ChristopherBrown200/f1-track-status-sign/3D Print Files/Tracks/Baku.stl

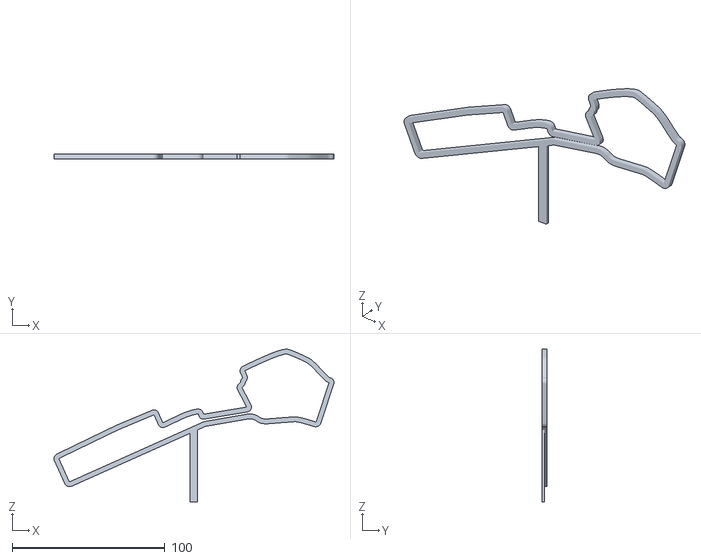
[picture p16: CAD file, 2026-06-22]
3D Print Files/Tracks/Baku.stl
183.3 x 3.00 x 100.0
