ChristopherBrown200/f1-track-status-sign/3D Print Files/Tracks/Gilles-Villeneuve.stl

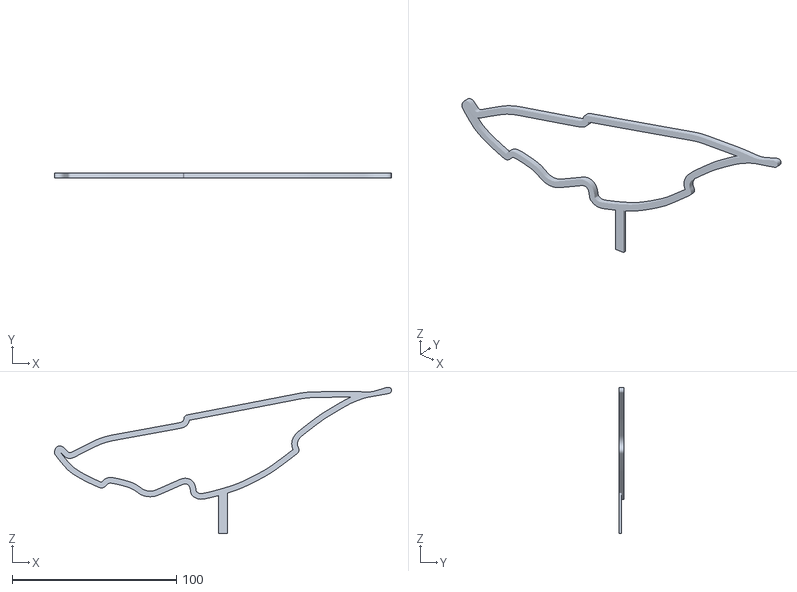
[picture p17: CAD file, 2026-06-22]
3D Print Files/Tracks/Gilles-Villeneuve.stl
204.9 x 3.00 x 89.0
