ChristopherBrown200/f1-track-status-sign/3D Print Files/Tracks/Zandvoort.stl

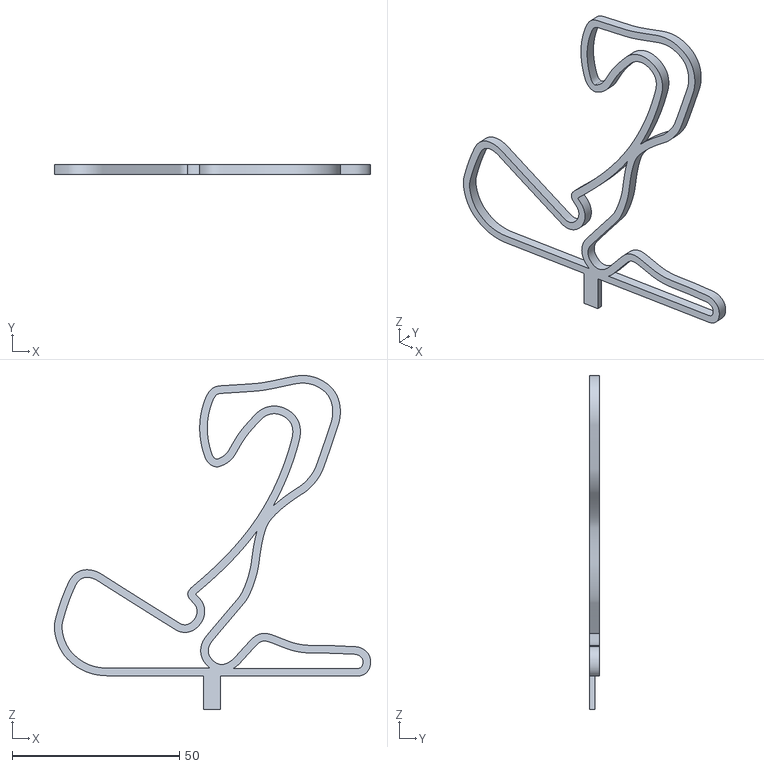
[picture p18: CAD file, 2026-06-22]
3D Print Files/Tracks/Zandvoort.stl
94.7 x 3.00 x 100.0
