ChristopherBrown200/f1-track-status-sign/3D Print Files/Tracks/Las Vegas.stl

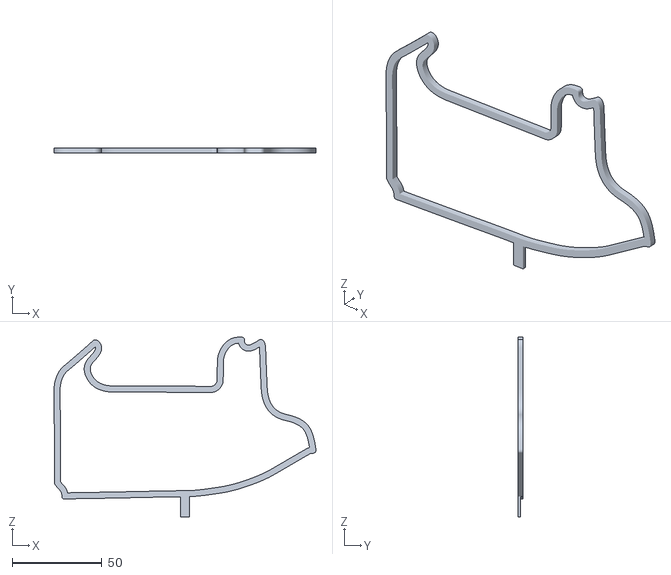
[picture p19: CAD file, 2026-06-22]
3D Print Files/Tracks/Las Vegas.stl
145.7 x 3.00 x 100.0
