ChristopherBrown200/f1-track-status-sign/3D Print Files/Tracks/Monaco.stl

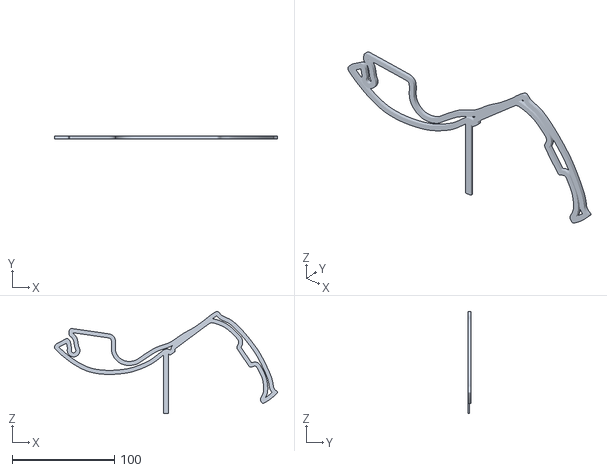
[picture p20: CAD file, 2026-06-22]
3D Print Files/Tracks/Monaco.stl
218.5 x 3.00 x 100.0
