ChristopherBrown200/f1-track-status-sign/3D Print Files/Tracks/Spa.stl

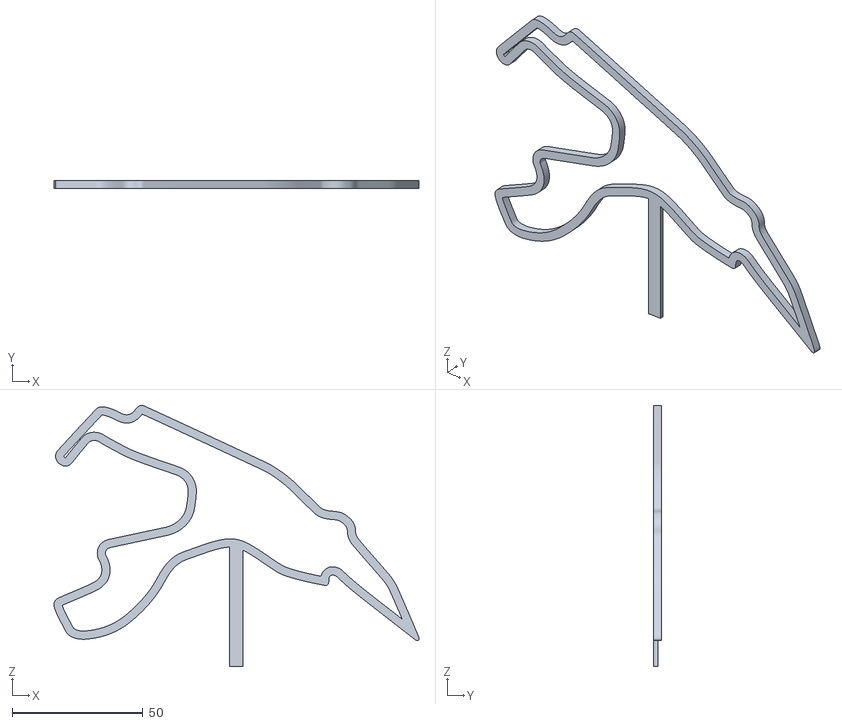
[picture p21: CAD file, 2026-06-22]
3D Print Files/Tracks/Spa.stl
139.7 x 3.00 x 100.0
