ChristopherBrown200/f1-track-status-sign/3D Print Files/Tracks/Silverstone.stl

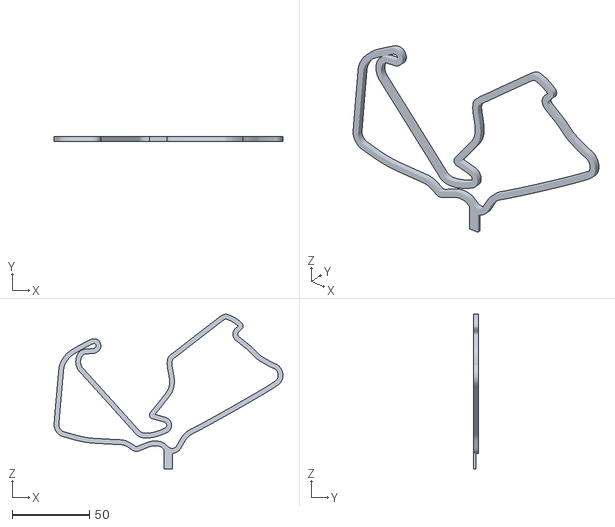
[picture p22: CAD file, 2026-06-22]
3D Print Files/Tracks/Silverstone.stl
148.1 x 3.00 x 100.0
