ChristopherBrown200/f1-track-status-sign/3D Print Files/Tracks/Albert Park.stl

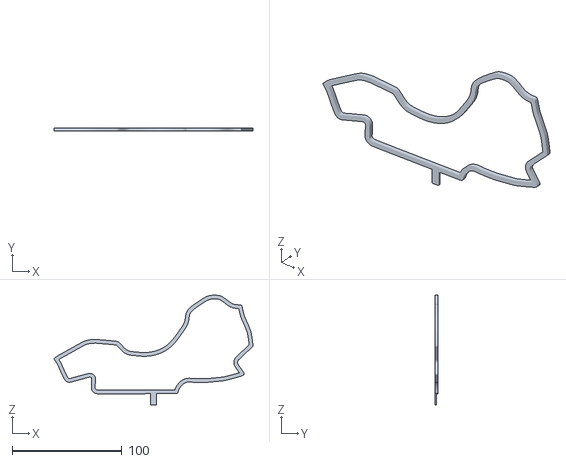
[picture p23: CAD file, 2026-06-22]
3D Print Files/Tracks/Albert Park.stl
181.4 x 3.00 x 100.0
