ChristopherBrown200/f1-track-status-sign/3D Print Files/Tracks/Suzuka.stl

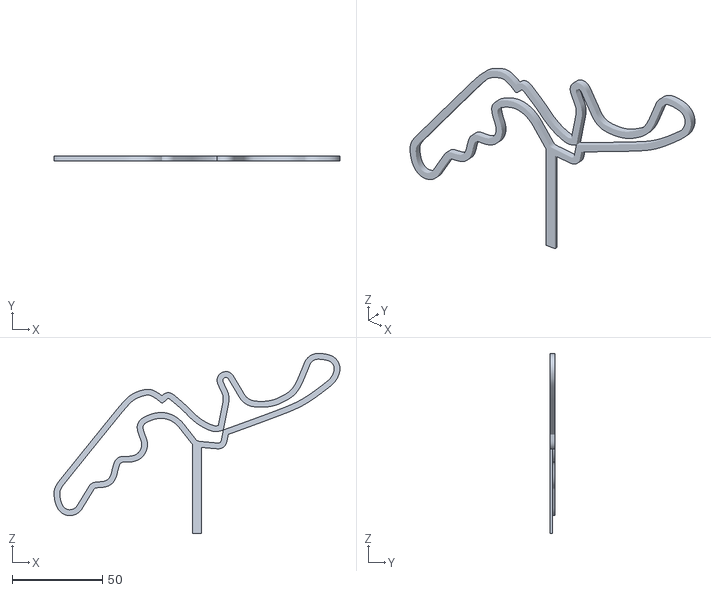
[picture p24: CAD file, 2026-06-22]
3D Print Files/Tracks/Suzuka.stl
158.7 x 3.00 x 100.0
