ChristopherBrown200/f1-track-status-sign/3D Print Files/Tracks/Istanbul Park.stl

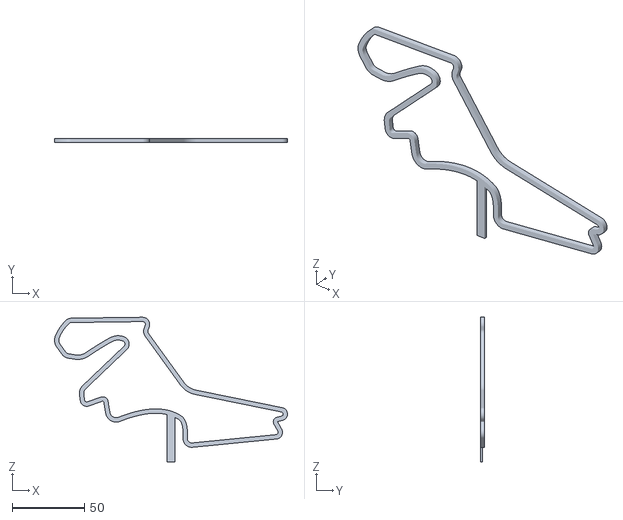
[picture p25: CAD file, 2026-06-22]
3D Print Files/Tracks/Istanbul Park.stl
161.2 x 3.00 x 100.0
