ChristopherBrown200/f1-track-status-sign/3D Print Files/Tracks/Madring.stl

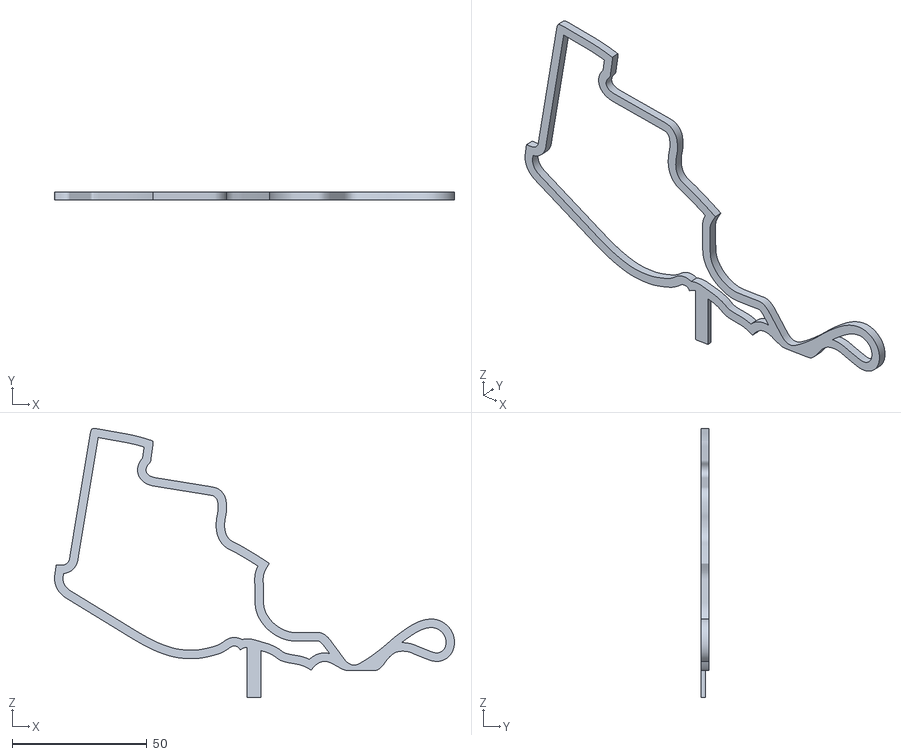
[picture p26: CAD file, 2026-06-22]
3D Print Files/Tracks/Madring.stl
148.7 x 3.00 x 100.0
