ChristopherBrown200/f1-track-status-sign/3D Print Files/Tracks/Marina Bay.stl

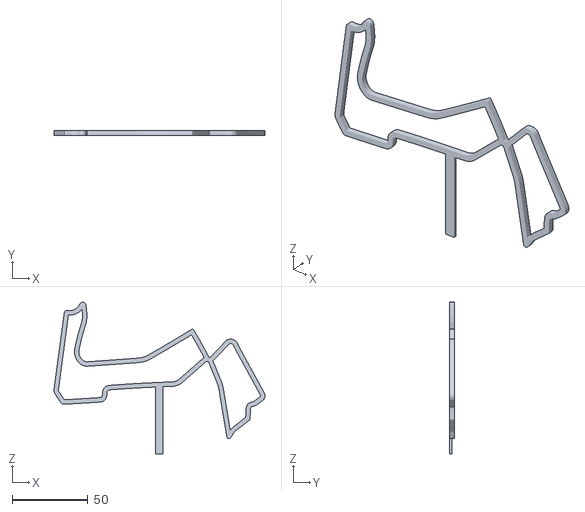
[picture p27: CAD file, 2026-06-22]
3D Print Files/Tracks/Marina Bay.stl
139.2 x 3.00 x 100.0
