ChristopherBrown200/f1-track-status-sign/3D Print Files/Tracks/Barcelona-Catalunya.stl

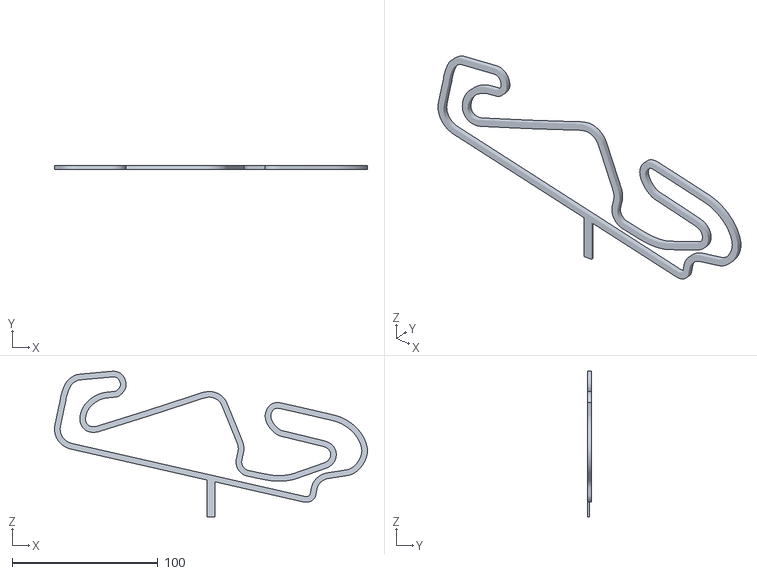
[picture p28: CAD file, 2026-06-22]
3D Print Files/Tracks/Barcelona-Catalunya.stl
215.0 x 3.00 x 100.0
