ChristopherBrown200/f1-track-status-sign/3D Print Files/Tracks/Red Bull Ring.stl

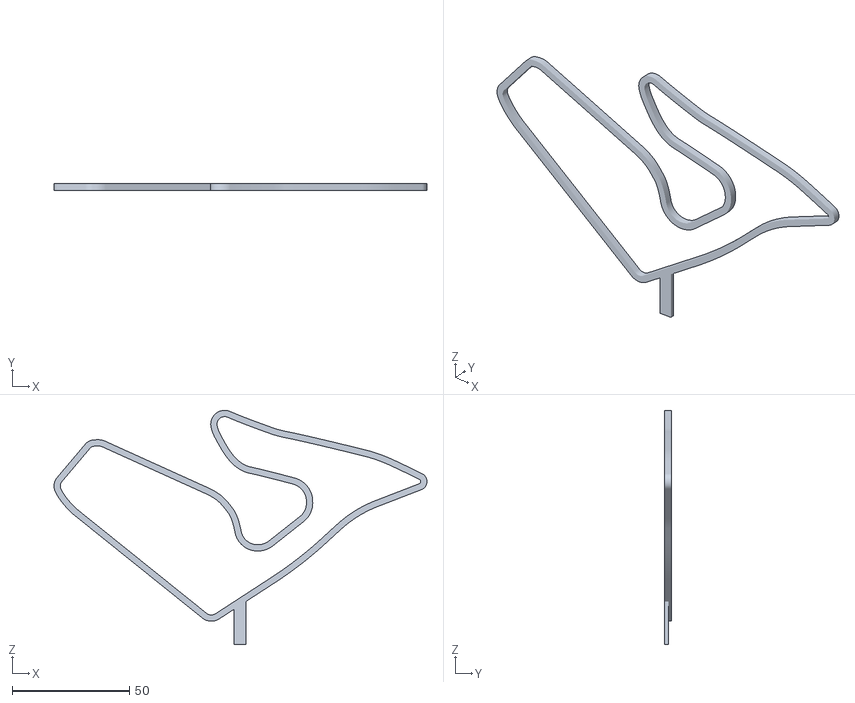
[picture p29: CAD file, 2026-06-22]
3D Print Files/Tracks/Red Bull Ring.stl
159.2 x 2.84 x 100.0
